mskurnik/PortablePacketStation/renders/Correctly Sized Case v21 - Case.png

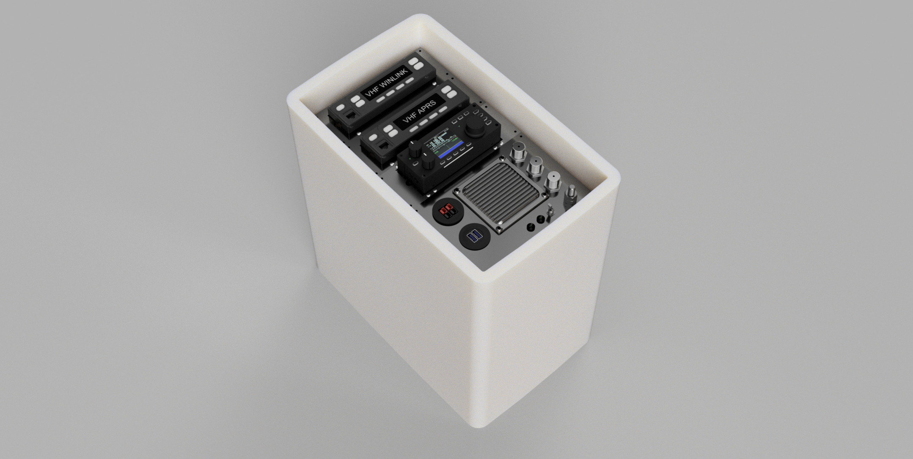
renders/Correctly Sized Case v21 - Case.png
