mskurnik/PortablePacketStation/renders/Small Kenwood Radio v20.png

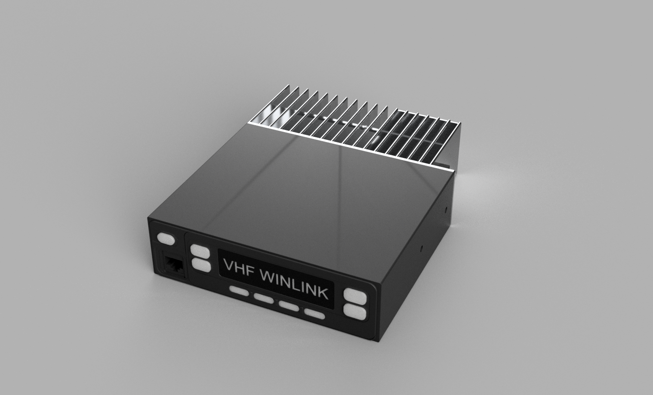
renders/Small Kenwood Radio v20.png
